rebeccajennifer/color-clock/docs/slide-decks/2026-05-05__engineering-talk/07__deployment__eng-talk/IMG_2154.jpeg

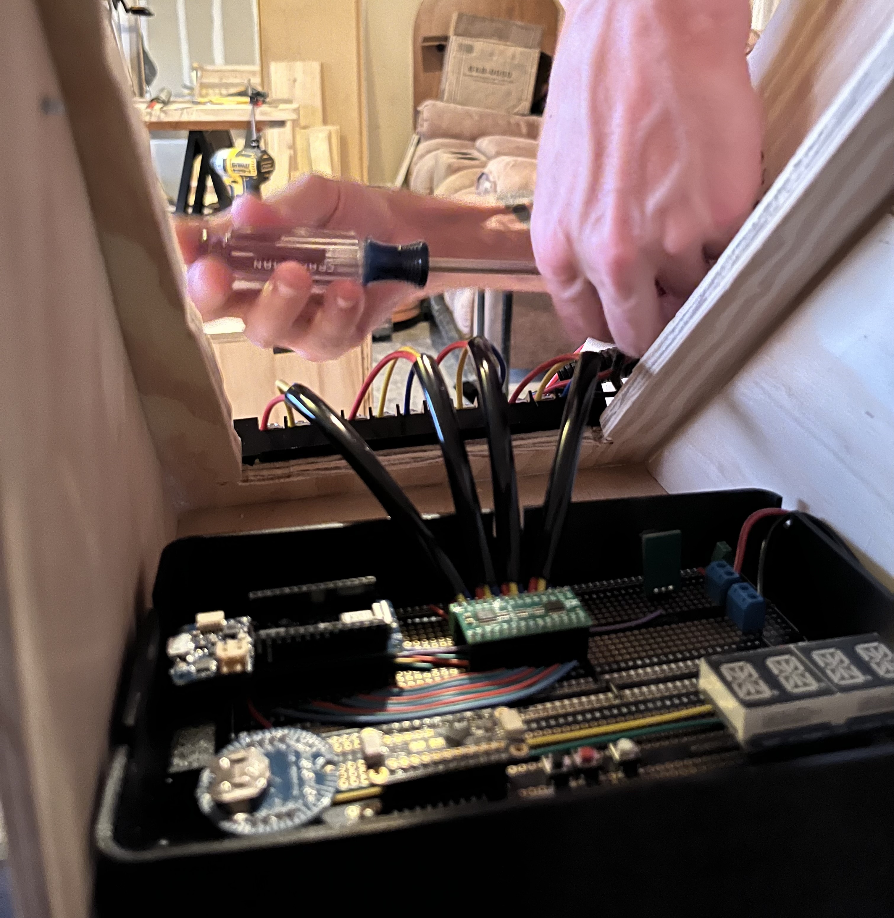
docs/slide-decks/2026-05-05__engineering-talk/07__deployment__eng-talk/IMG_2154.jpeg
