rebeccajennifer/color-clock/docs/slide-decks/2024-08-10__demo/_photos-demo/circuit-board-final.jpeg

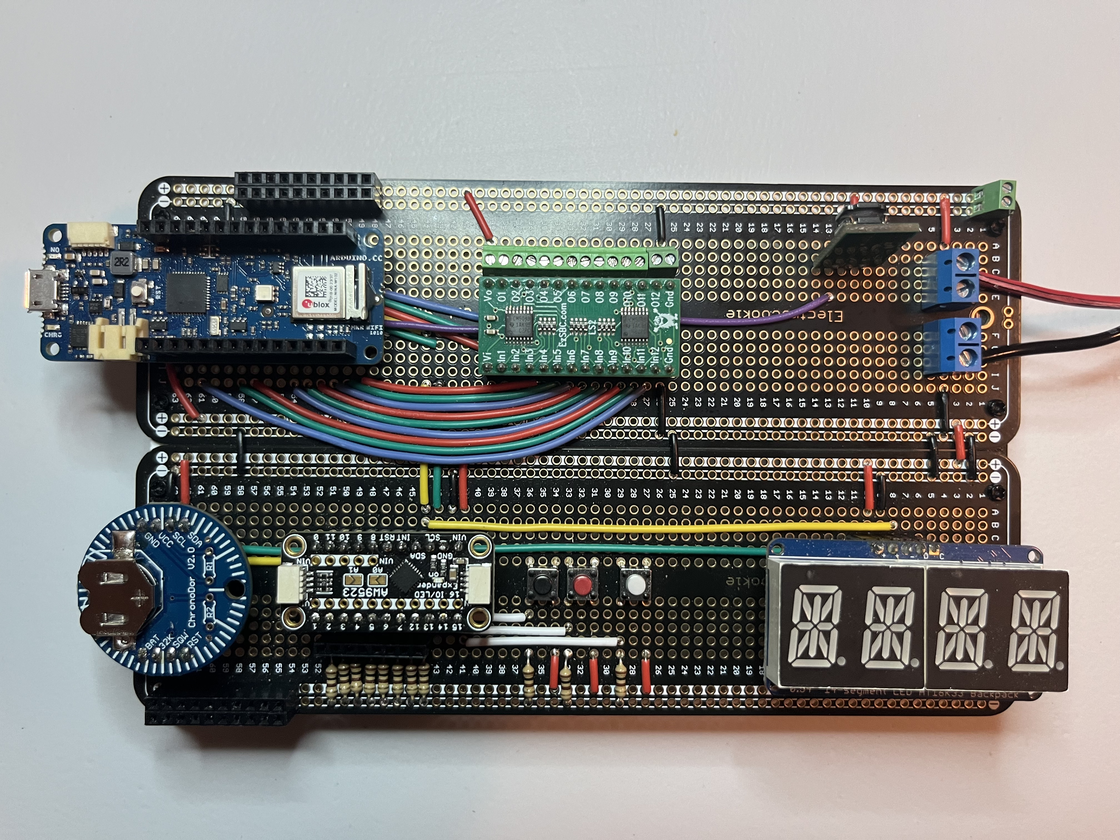
docs/slide-decks/2024-08-10__demo/_photos-demo/circuit-board-final.jpeg
