rebeccajennifer/color-clock/docs/slide-decks/2026-05-05__engineering-talk/04__light-display__eng-talk/acrylic-sheet-rev-a__2024-06-08.png

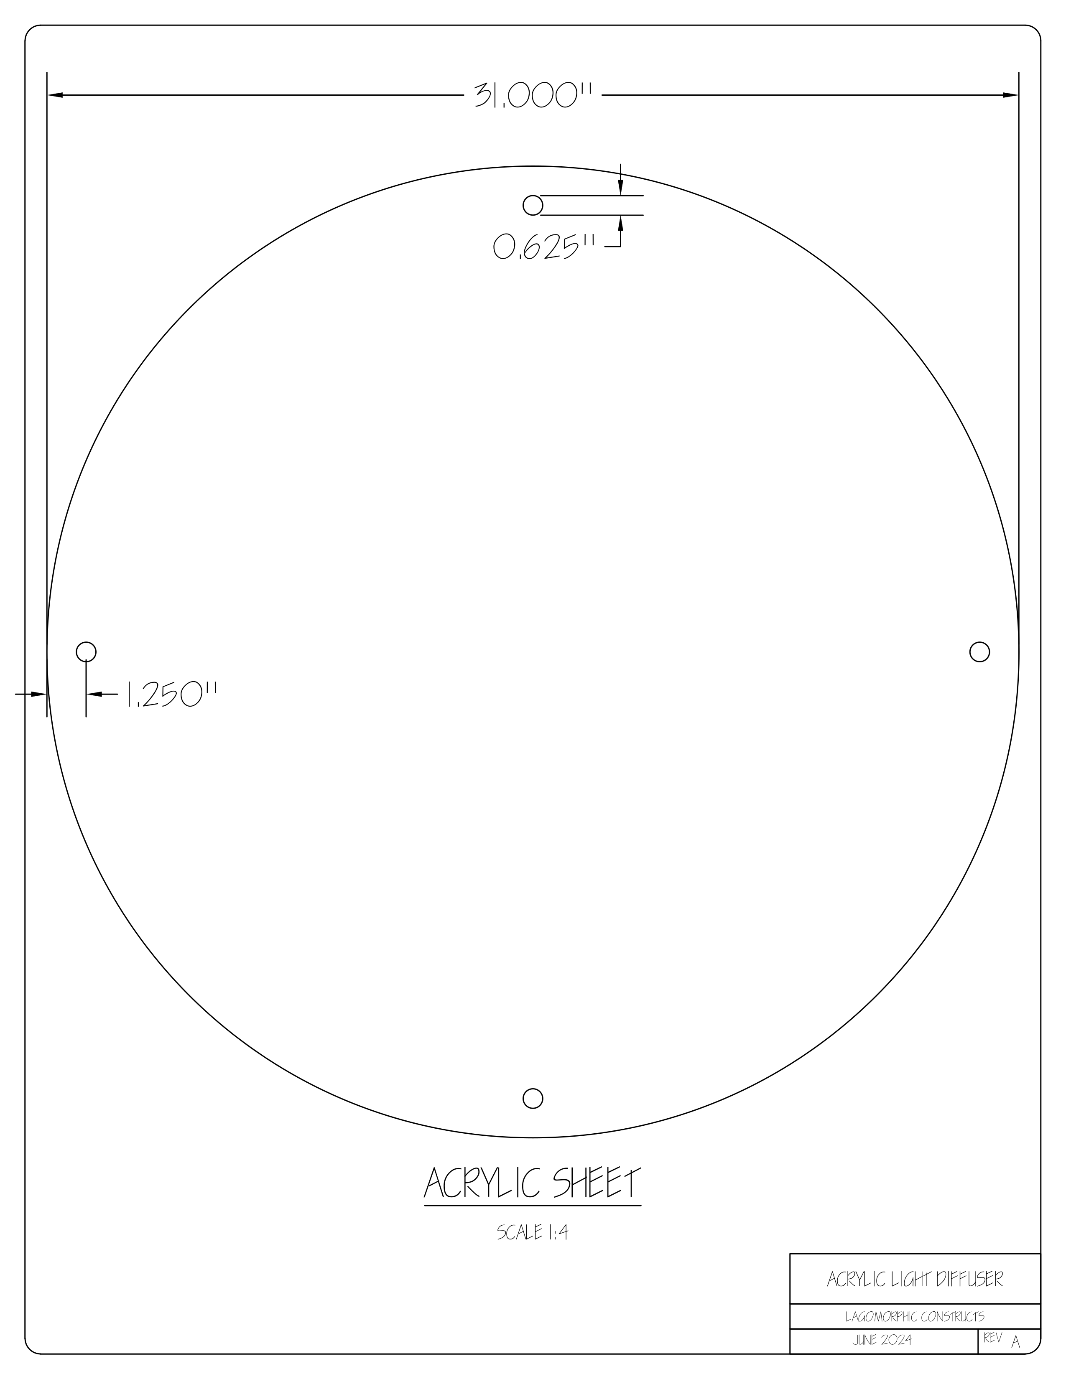
docs/slide-decks/2026-05-05__engineering-talk/04__light-display__eng-talk/acrylic-sheet-rev-a__2024-06-08.png
