rebeccajennifer/color-clock/docs/slide-decks/2026-05-05__engineering-talk/05__user-interface__eng-talk/user-ctrl-prototype-cardboard.jpeg

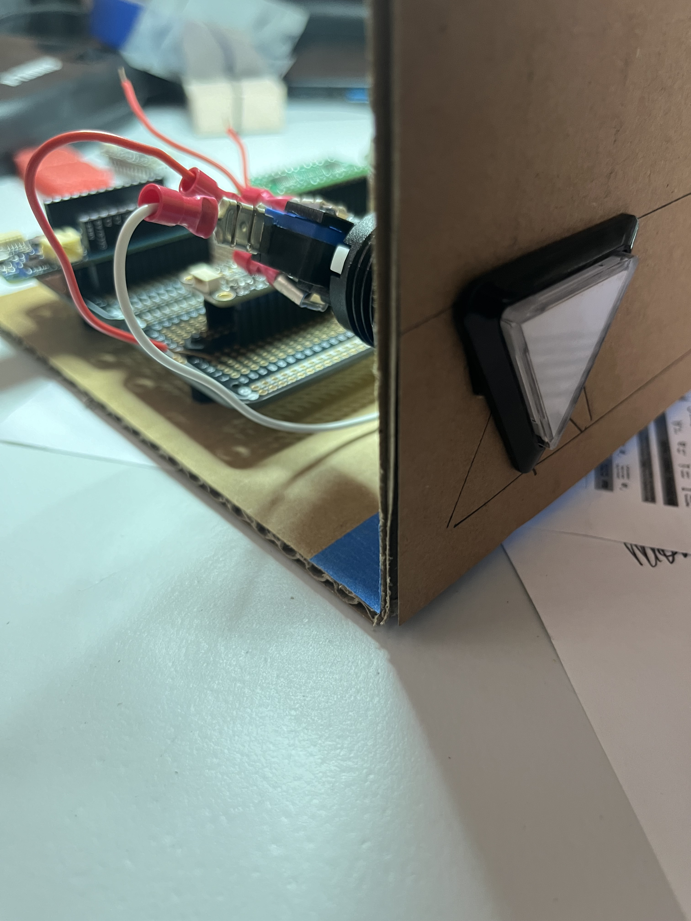
docs/slide-decks/2026-05-05__engineering-talk/05__user-interface__eng-talk/user-ctrl-prototype-cardboard.jpeg
