rebeccajennifer/color-clock/docs/slide-decks/2026-05-05__engineering-talk/06__circuit-board-evolution__eng-talk/IMG_2068.JPEG

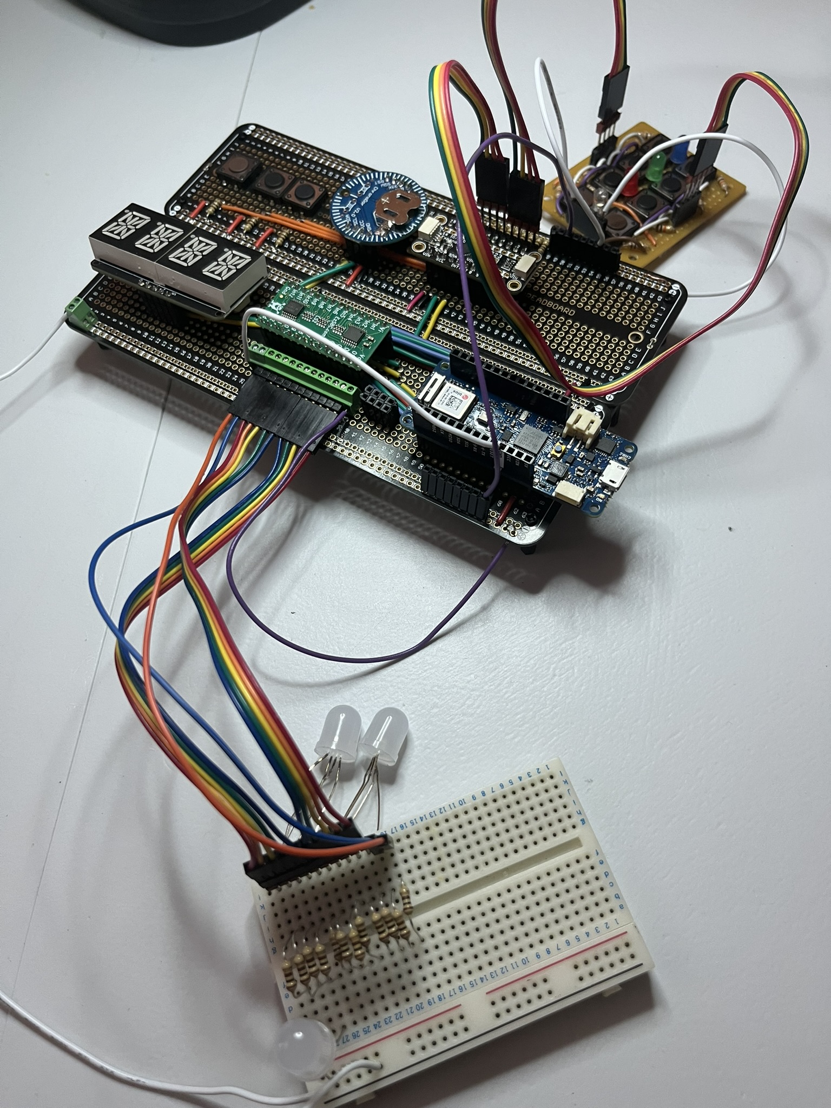
docs/slide-decks/2026-05-05__engineering-talk/06__circuit-board-evolution__eng-talk/IMG_2068.JPEG
