rebeccajennifer/color-clock/docs/slide-decks/2026-05-05__engineering-talk/07__deployment__eng-talk/solar__eng-talk/IMG_2150.JPEG

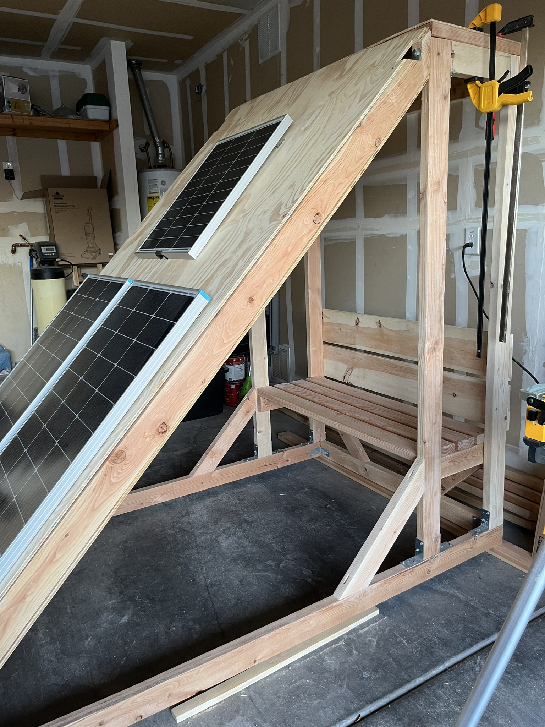
docs/slide-decks/2026-05-05__engineering-talk/07__deployment__eng-talk/solar__eng-talk/IMG_2150.JPEG
