rebeccajennifer/color-clock/docs/slide-decks/2026-05-05__engineering-talk/07__deployment__eng-talk/structure-00__initial__eng-talk/napkin-sketch.jpeg

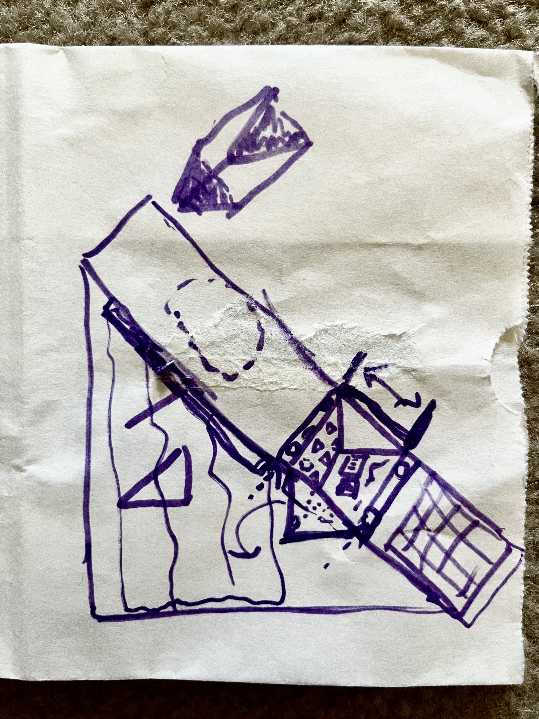
docs/slide-decks/2026-05-05__engineering-talk/07__deployment__eng-talk/structure-00__initial__eng-talk/napkin-sketch.jpeg
