rebeccajennifer/color-clock/docs/slide-decks/2026-05-05__engineering-talk/08__final-thoughts__eng-talk/qr-source-code.png

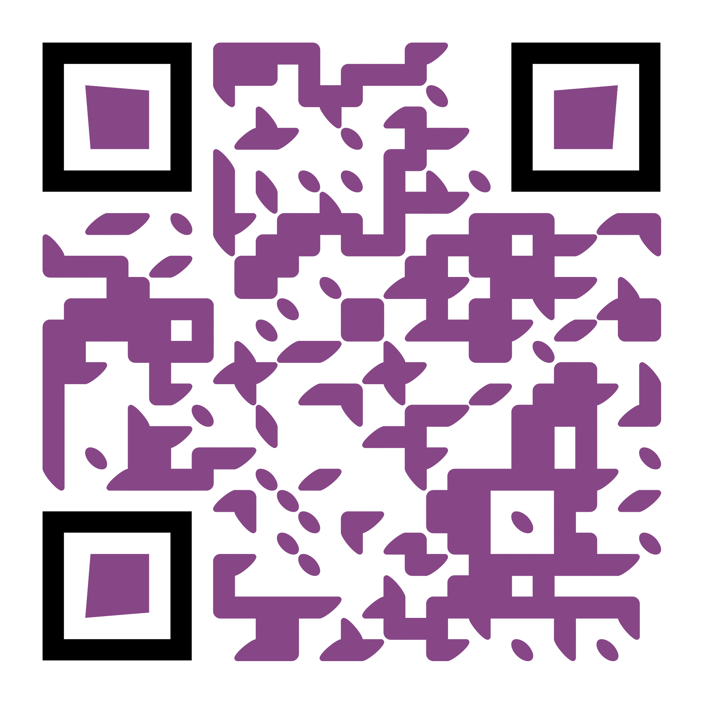
docs/slide-decks/2026-05-05__engineering-talk/08__final-thoughts__eng-talk/qr-source-code.png
