rebeccajennifer/color-clock/docs/sw-docs/plant-uml/bitmap-img__puml/0-state-top-level.png

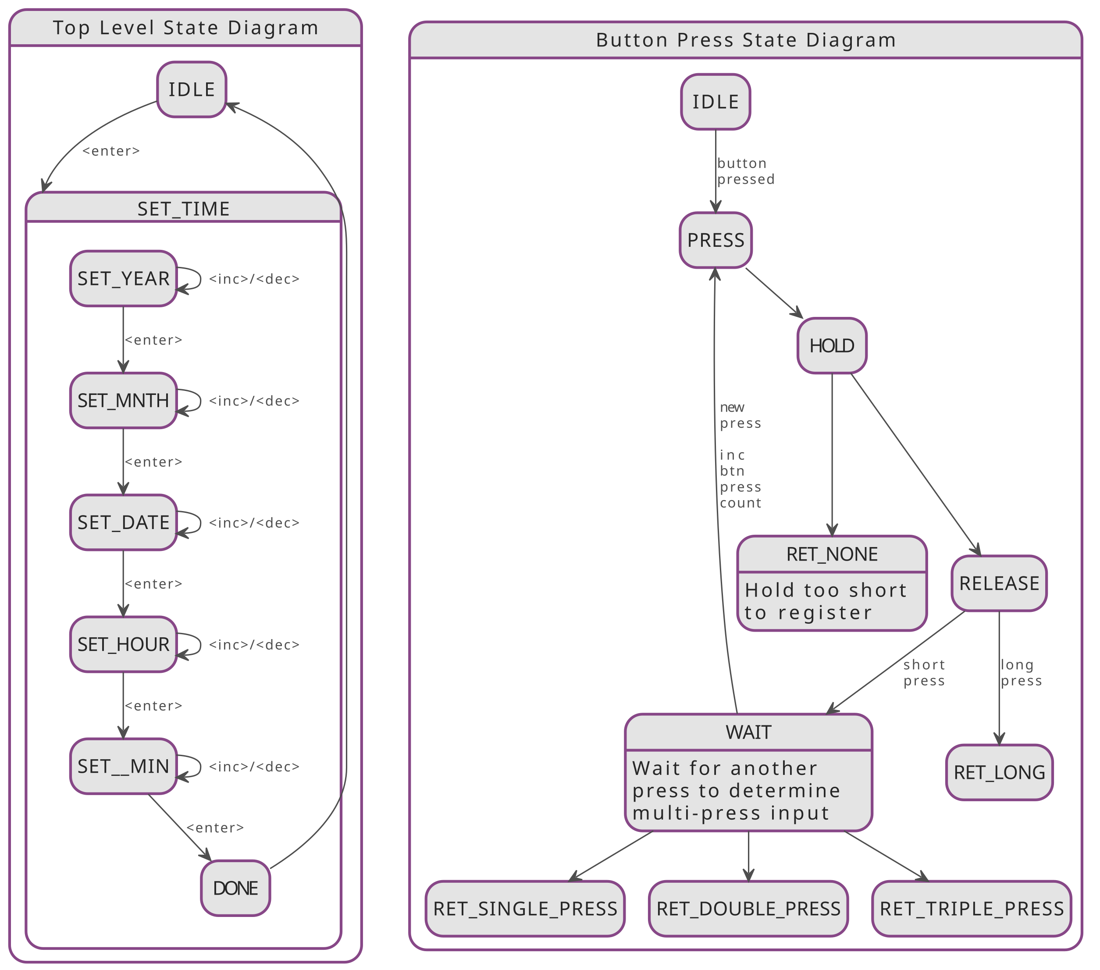
docs/sw-docs/plant-uml/bitmap-img__puml/0-state-top-level.png
