rebeccajennifer/color-clock/docs/sw-docs/plant-uml/bitmap-img__puml/1-class-user-ctrl.png

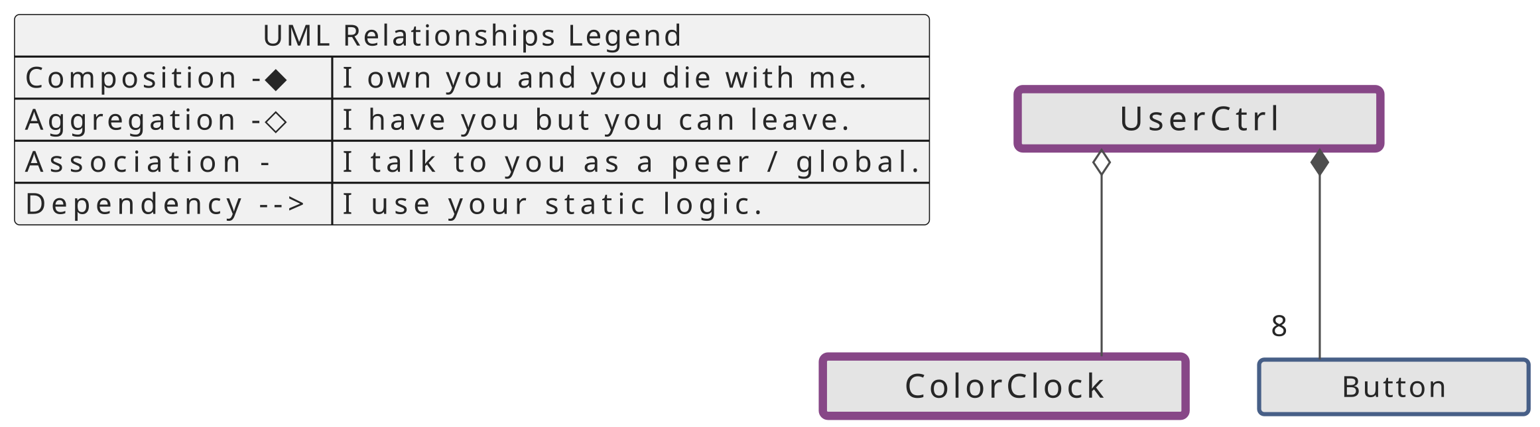
docs/sw-docs/plant-uml/bitmap-img__puml/1-class-user-ctrl.png
