rebeccajennifer/color-clock/docs/sw-docs/plant-uml/bitmap-img__puml/2-class-time-ctrl.png

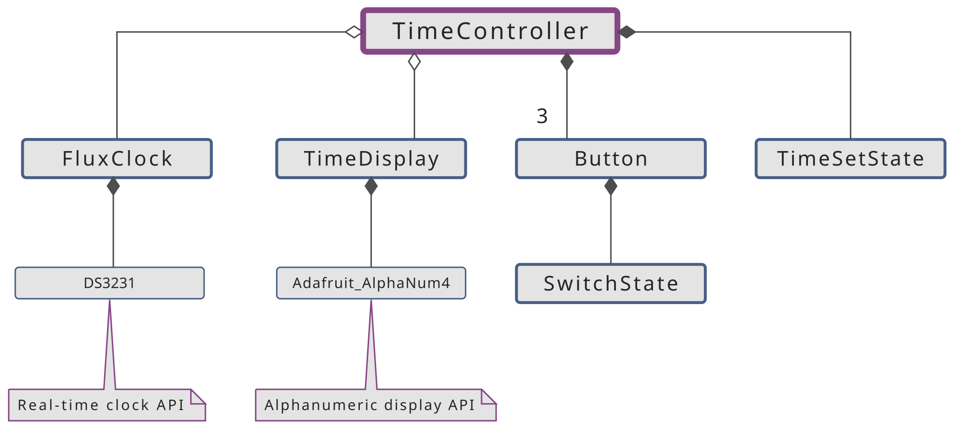
docs/sw-docs/plant-uml/bitmap-img__puml/2-class-time-ctrl.png
