rebeccajennifer/color-clock/docs/sw-docs/plant-uml/bitmap-img__puml/3-class-color-clock.png

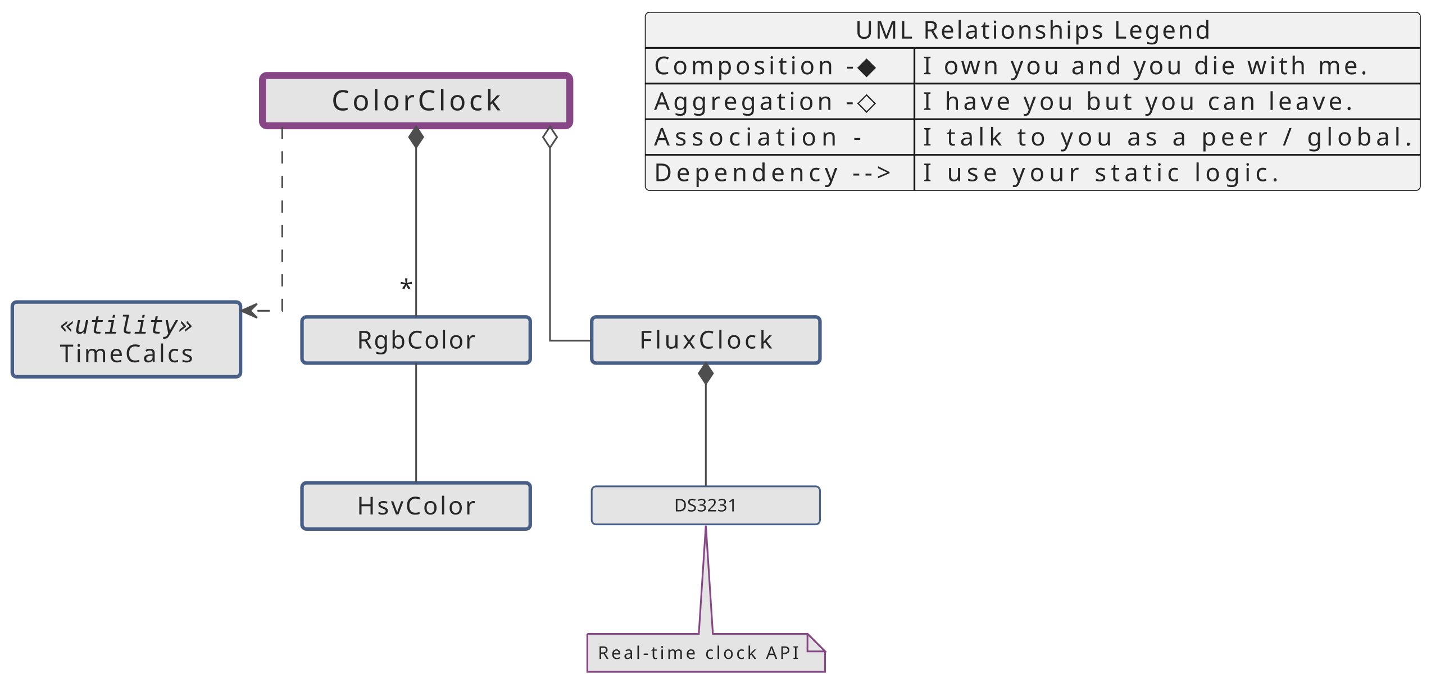
docs/sw-docs/plant-uml/bitmap-img__puml/3-class-color-clock.png
