rebeccajennifer/color-clock/docs/sw-docs/plant-uml/bitmap-img__puml/3-data-path-color-clock.png

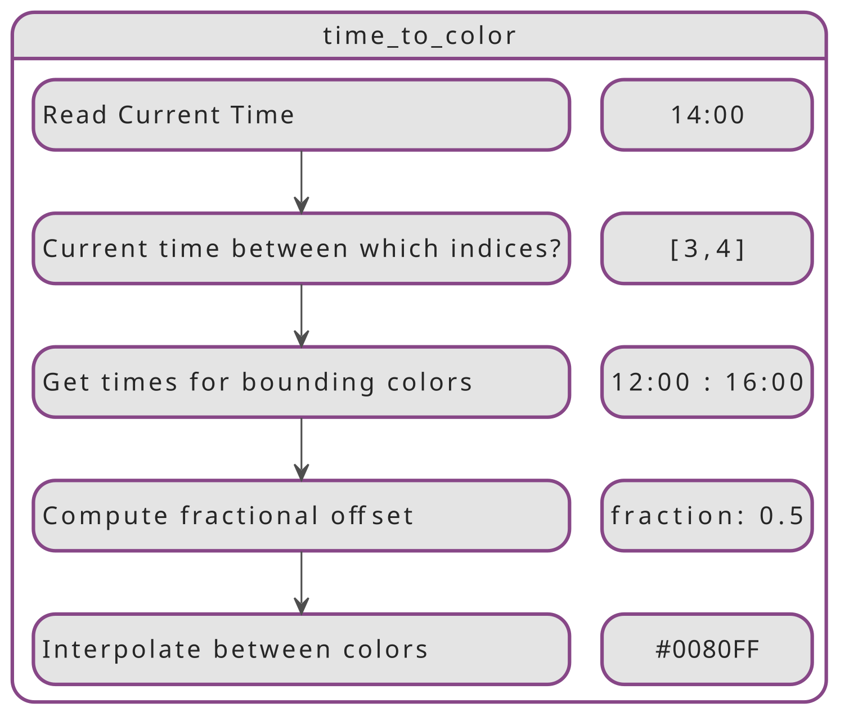
docs/sw-docs/plant-uml/bitmap-img__puml/3-data-path-color-clock.png
