rebeccajennifer/color-clock/docs/sw-docs/plant-uml/bitmap-img__puml/legend.png

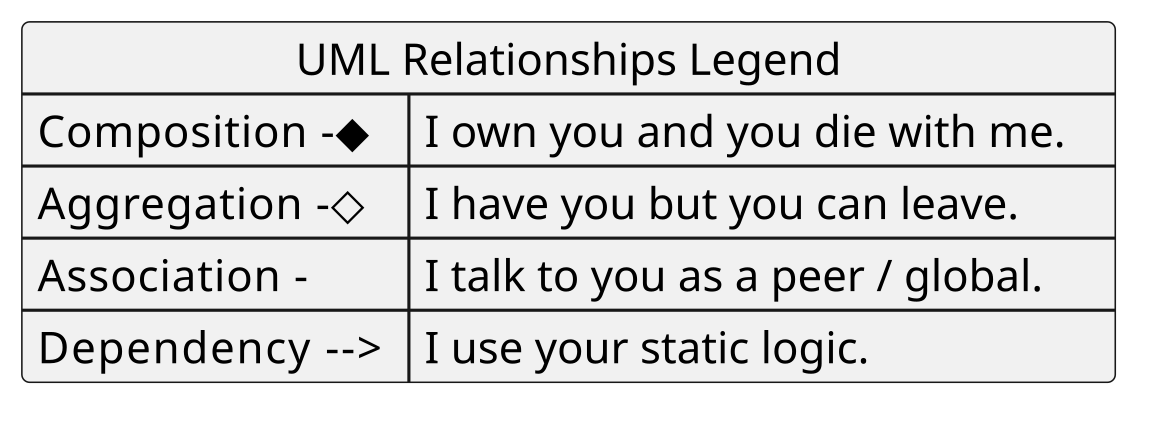
docs/sw-docs/plant-uml/bitmap-img__puml/legend.png
