rebeccajennifer/color-clock/docs/slide-decks/2026-05-05__engineering-talk/04__light-display__eng-talk/IMG_1861.jpeg

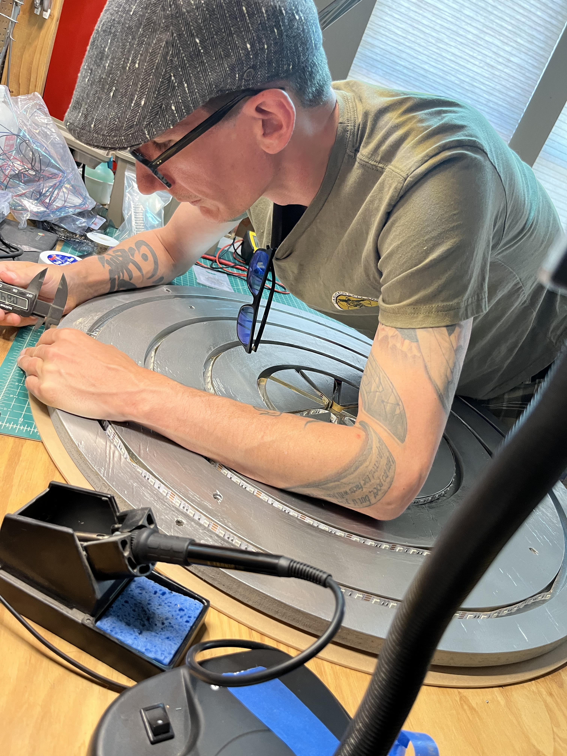
docs/slide-decks/2026-05-05__engineering-talk/04__light-display__eng-talk/IMG_1861.jpeg
